monsonite/Byter/74HC283_logic.jpg

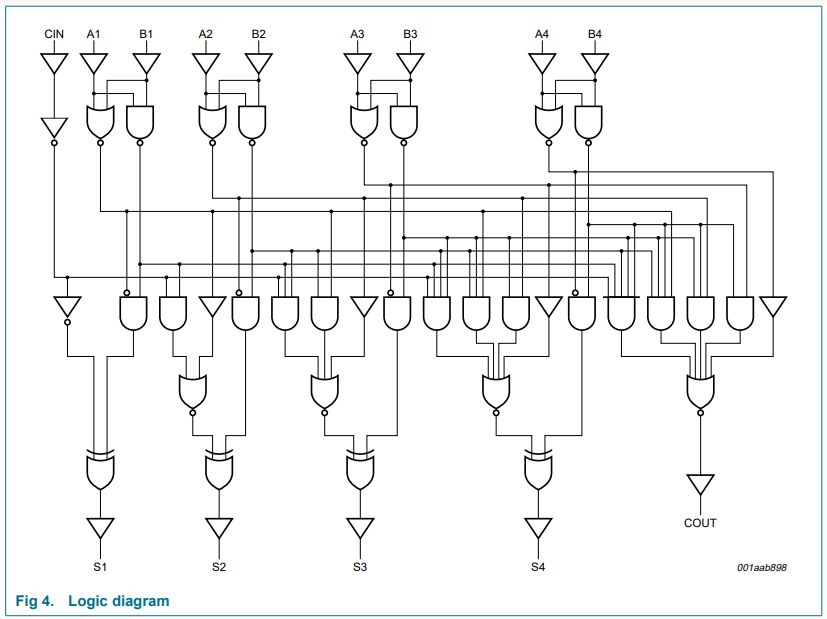
74HC283_logic.jpg
