monsonite/Byter/74126_ALU_mux.jpg

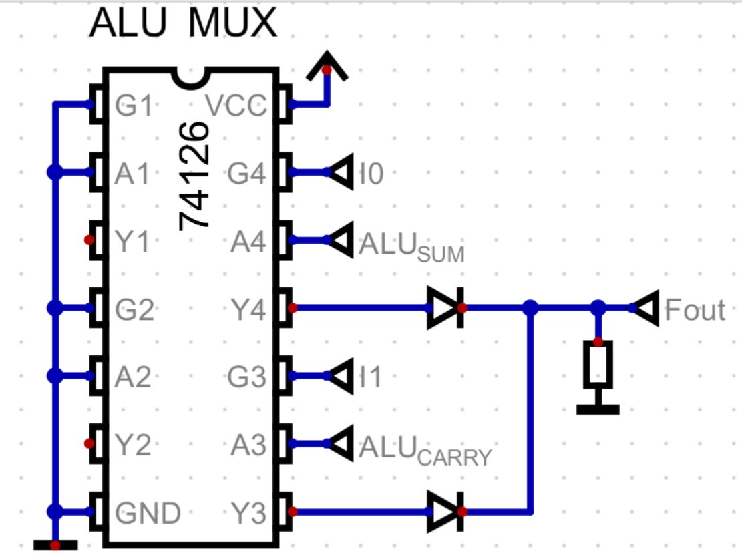
74126_ALU_mux.jpg
