monsonite/Byter/BYTER_02.jpg

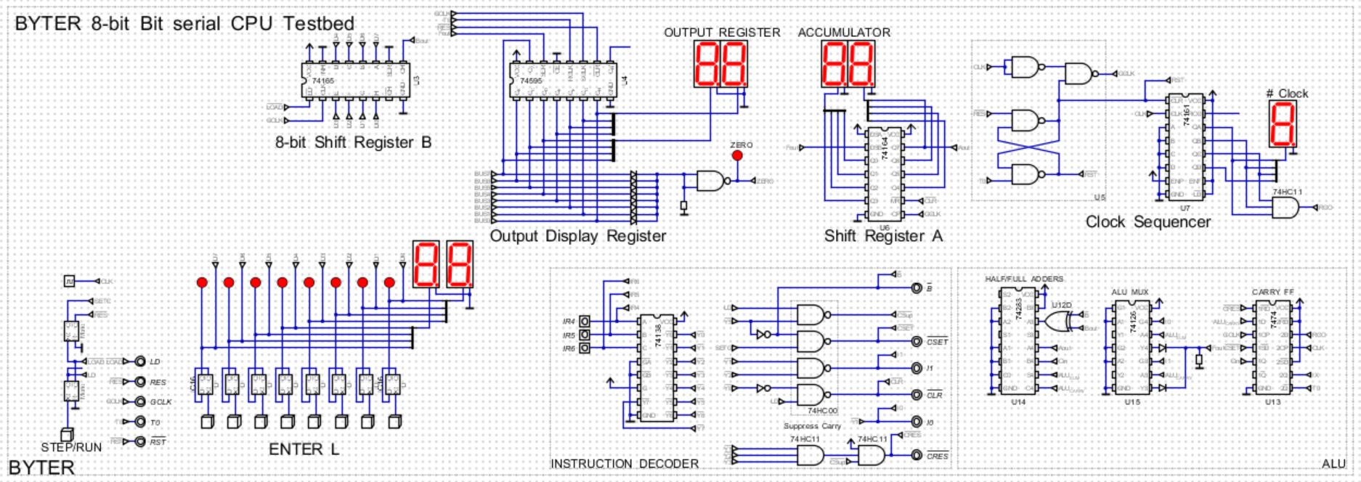
BYTER_02.jpg
