monsonite/Byter/byter_74HC299_Accumulator.jpg

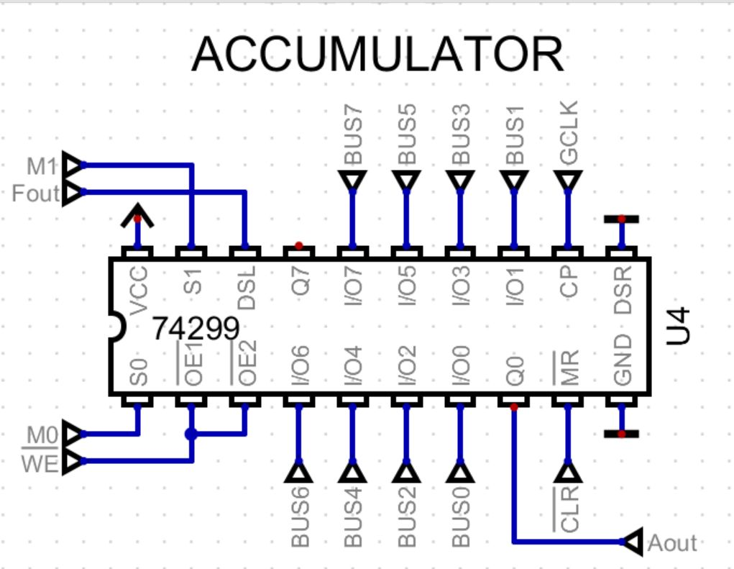
byter_74HC299_Accumulator.jpg
