monsonite/Byter/Byter_283_adders.jpg

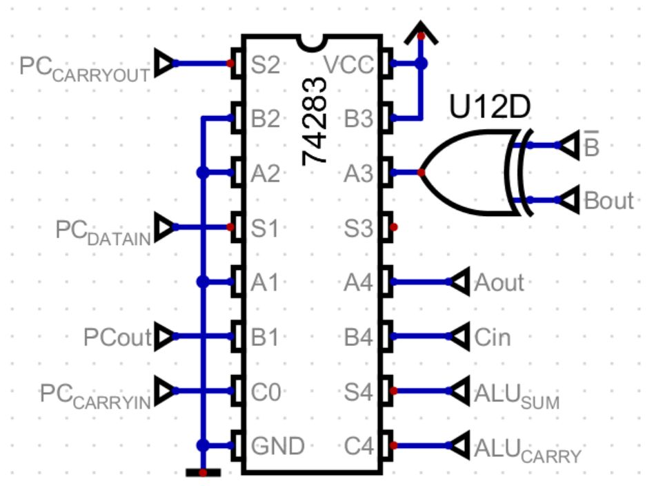
Byter_283_adders.jpg
