monsonite/Byter/Byter_ALU_01.jpg

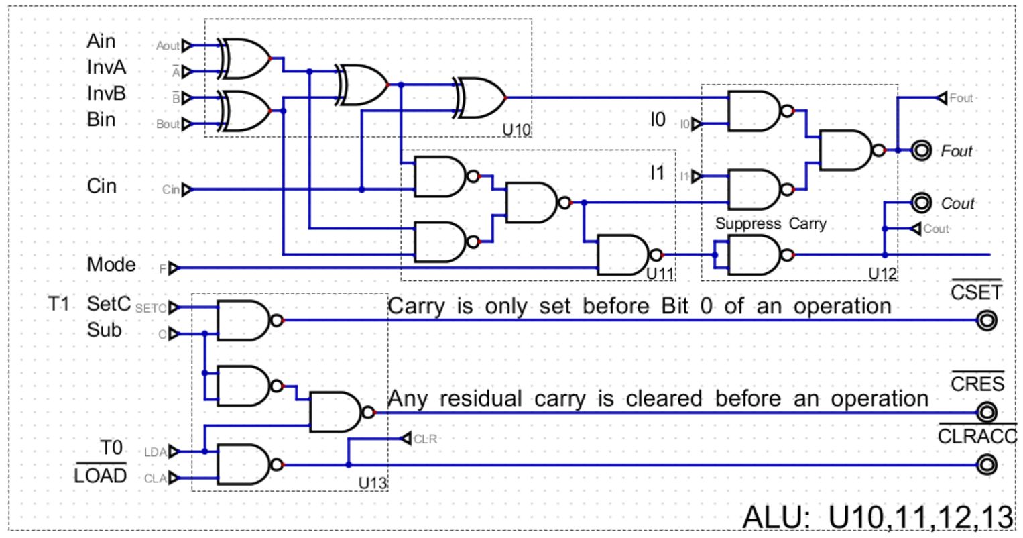
Byter_ALU_01.jpg
