monsonite/Byter/Byter_clock_seq_01.jpg

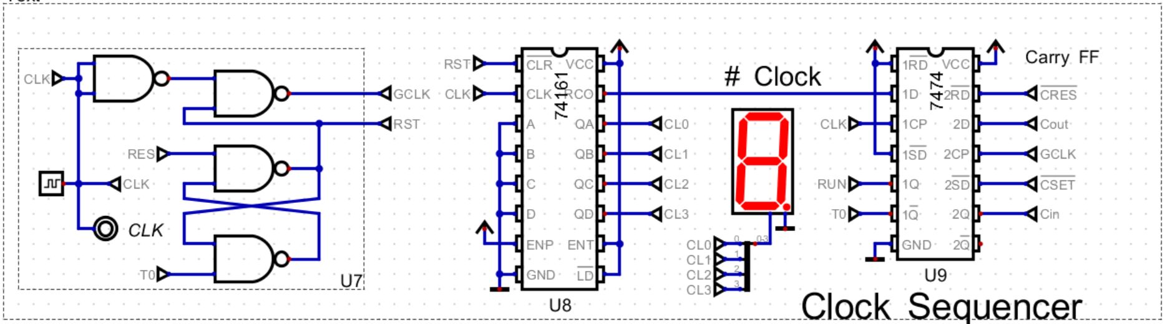
Byter_clock_seq_01.jpg
