monsonite/Byter/byter_clock_sequencer_pc.jpg

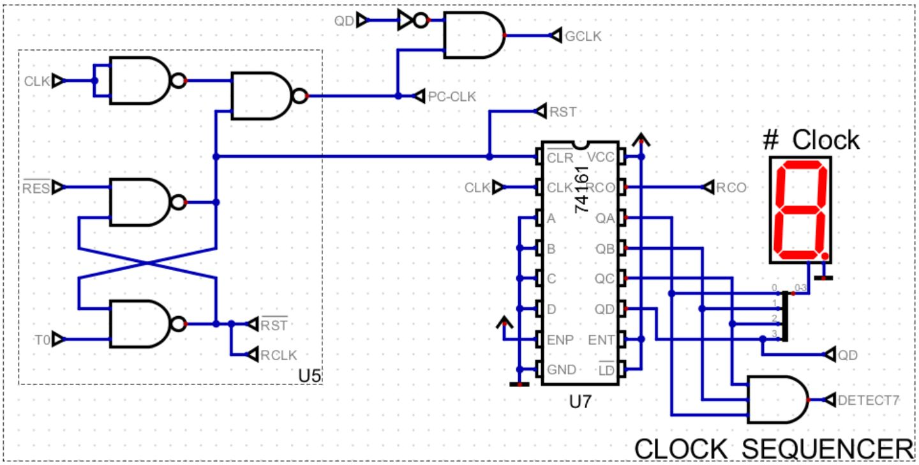
byter_clock_sequencer_pc.jpg
