monsonite/Byter/shrek_3D.jpg

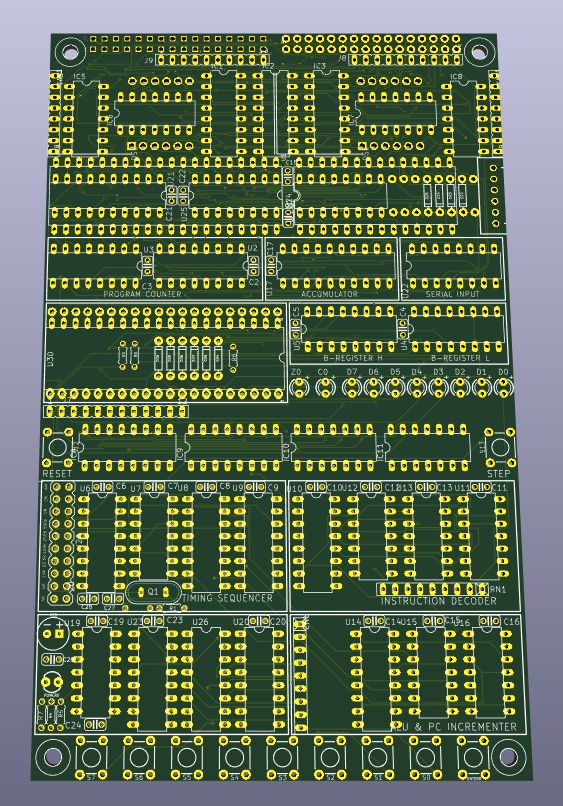
shrek_3D.jpg
