monsonite/Byter/shrek_layout_30_7_24.jpg

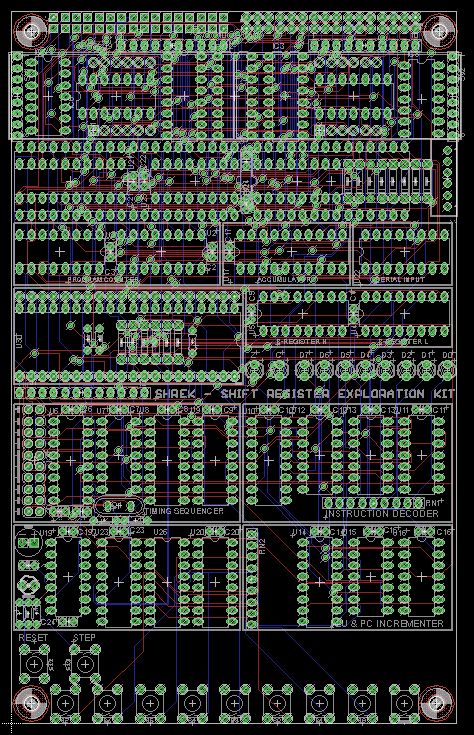
shrek_layout_30_7_24.jpg
