monsonite/Byter/byter_instruction_decoder.jpg

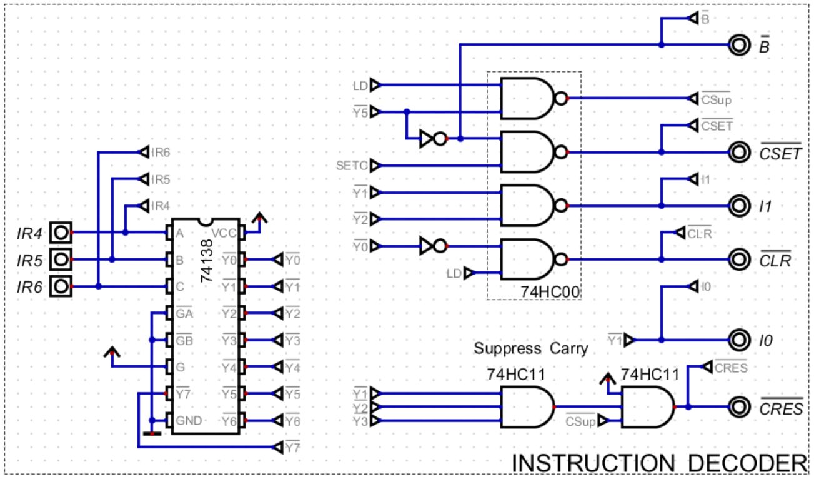
byter_instruction_decoder.jpg
